DigKleppe/ESP32thermometer3/hardware/thermometer.kicad_sch

## KiCad design hardware/thermometer.kicad_sch (2025-02-03)

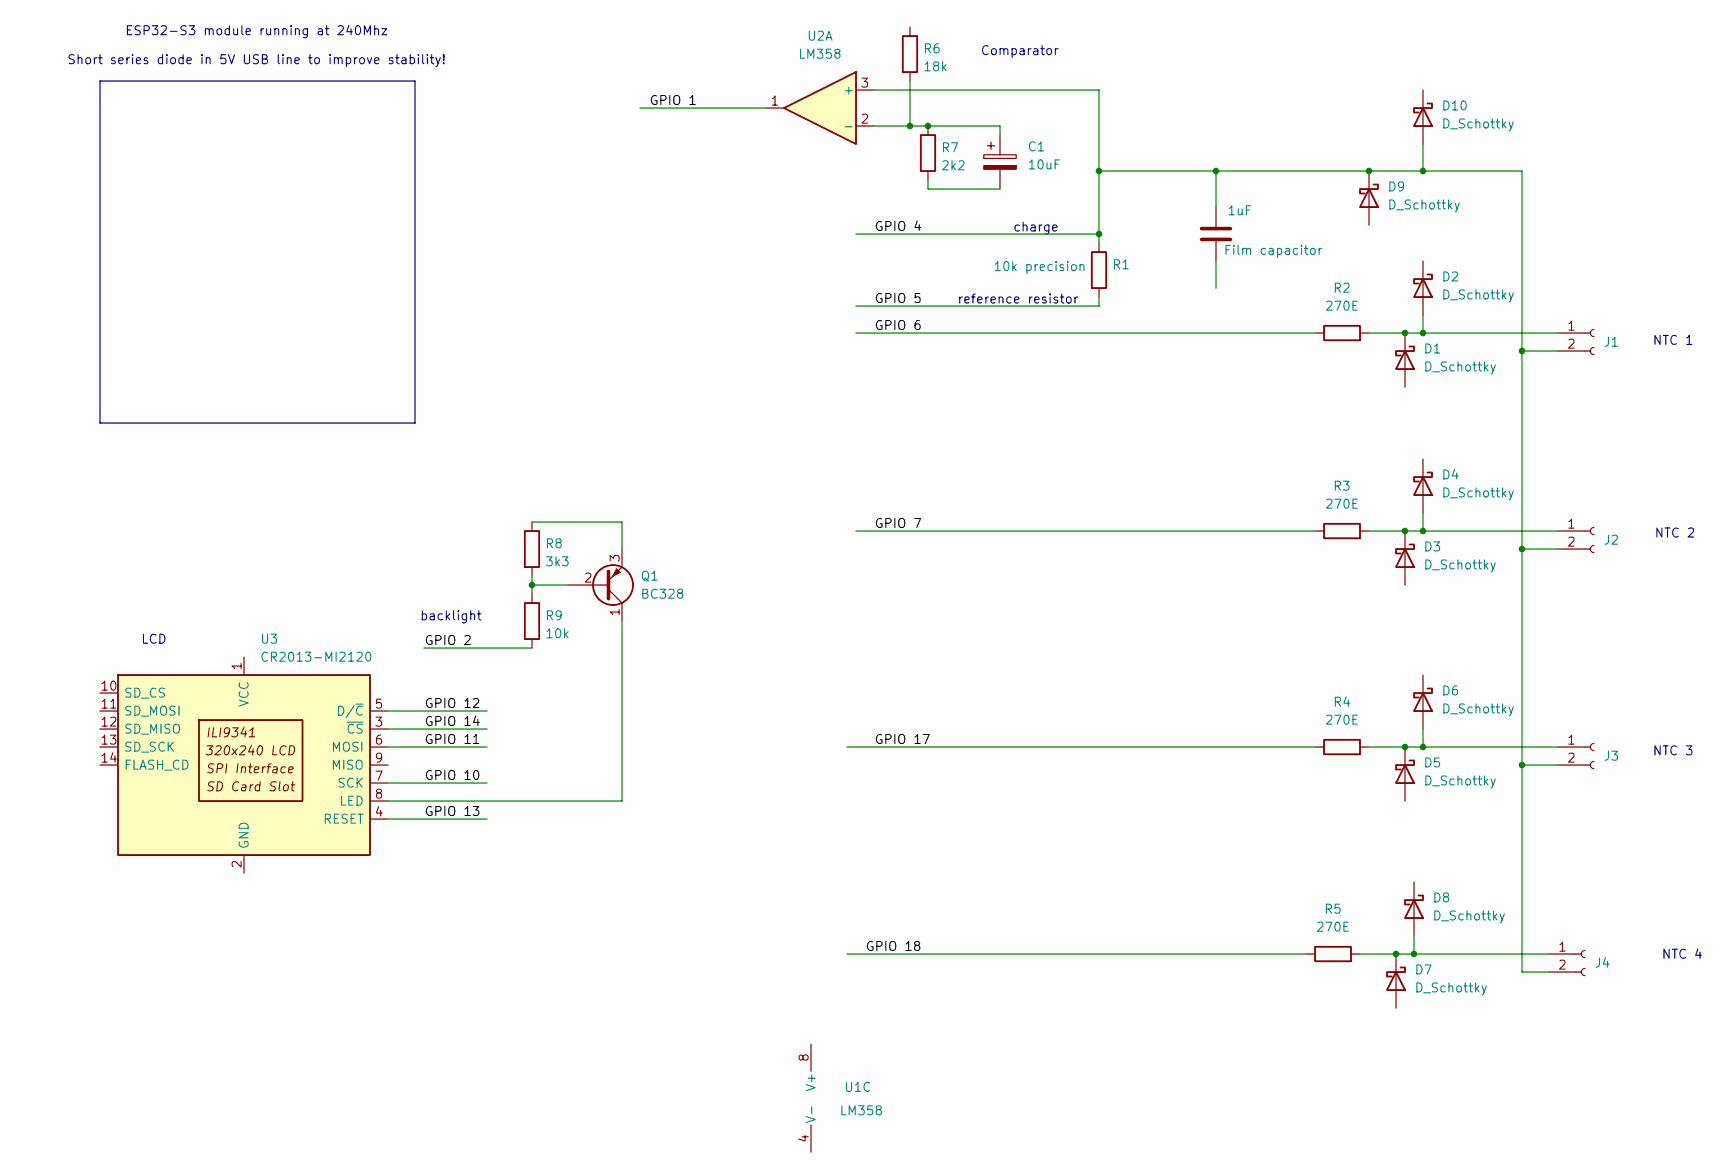
[picture p2: schematic thermometer.kicad_sch]

Parts:
1uF: Film capacitor
C1: 10uF
D1, D2, D3, D4, D5, D6, D7, D8, D9, D10: D_Schottky
J1, J2, J3, J4: Conn_01x02_Socket
Q1: BC328; TO-92_Inline
R1: 10k precision
R2, R3, R4, R5: 270E
R6: 18k
R7: 2k2
R8: 3k3
R9: 10k
U1, U2: LM358
U3: CR2013-MI2120

Connections:
GPIO 1: U2.1
GPIO 2: R9.2
GPIO 4: 1uF.1, D9.1 (K), D10.2 (A), J1.2, J2.2, J3.2, J4.2, R1.1, U2.3 (+)
GPIO 5: R1.2
GPIO 6: R2.1
GPIO 7: R3.1
GPIO 10: U3.7 (SCK)
GPIO 11: U3.6 (MOSI)
GPIO 12: U3.5 (D/~C)
GPIO 13: U3.4 (RESET)
GPIO 14: U3.3 (~CS)
GPIO 17: R4.1
GPIO 18: R5.1
unnamed: C1.1, R6.2, R7.1, U2.2 (-)
unnamed: C1.2, R7.2
unnamed: D1.1 (K), D2.2 (A), J1.1, R2.2
unnamed: D3.1 (K), D4.2 (A), J2.1, R3.2
unnamed: D5.1 (K), D6.2 (A), J3.1, R4.2
unnamed: D7.1 (K), D8.2 (A), J4.1, R5.2
unnamed: Q1.1 (C), U3.8 (LED)
unnamed: Q1.2 (B), R8.2, R9.1
unnamed: Q1.3 (E), R8.1

Notes on the sheet:
NTC 2
NTC 4
Comparator
NTC 3
NTC 1
reference resistor
ESP32-S3 module running at 240Mhz Short series diode in 5V USB line to improve stability!
charge
backlight
LCD
