DigKleppe/ESP32thermometer3/main/include/i2cTask.h

/*
 * i2cTask.h
 *
 *  Created on: Aug 9, 2021
 *      Author: dig
 *
 *      handles display and TMP117 (reference sensor)
 */

#ifndef MAIN_INCLUDE_I2CTASK_H_
#define MAIN_INCLUDE_I2CTASK_H_

#include "freertos/FreeRTOS.h"
#include "freertos/queue.h"
#include "freertos/task.h"

void I2CTask(void *arg);

extern QueueHandle_t displayMssgbox;

float getTmp117Temperature(void);
float getTmp117AveragedTemperature(void);

#endif /* MAIN_INCLUDE_I2CTASK_H_ */
