DigKleppe/ESP32thermometer3/main/include/stdev.h

/*
 * stdev.h
 *
 *  Created on: Dec 23, 2024
 *      Author: dig
 */

#ifndef MAIN_INCLUDE_STDEV_H_
#define MAIN_INCLUDE_STDEV_H_

float calculateStandardDeviation(int N, float data[]);

#endif /* MAIN_INCLUDE_STDEV_H_ */
